Fisherman166/GM_Burnoff_Module/pcb_pictures/20211124_192147.jpg

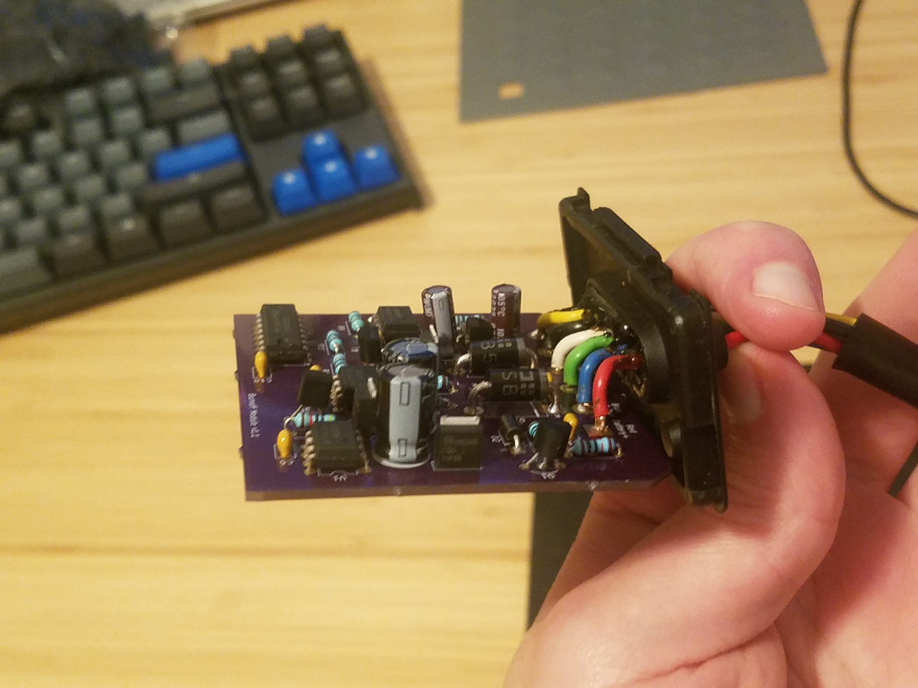
pcb_pictures/20211124_192147.jpg
