Fisherman166/GM_Burnoff_Module/pcb_pictures/20211023_175507.jpg

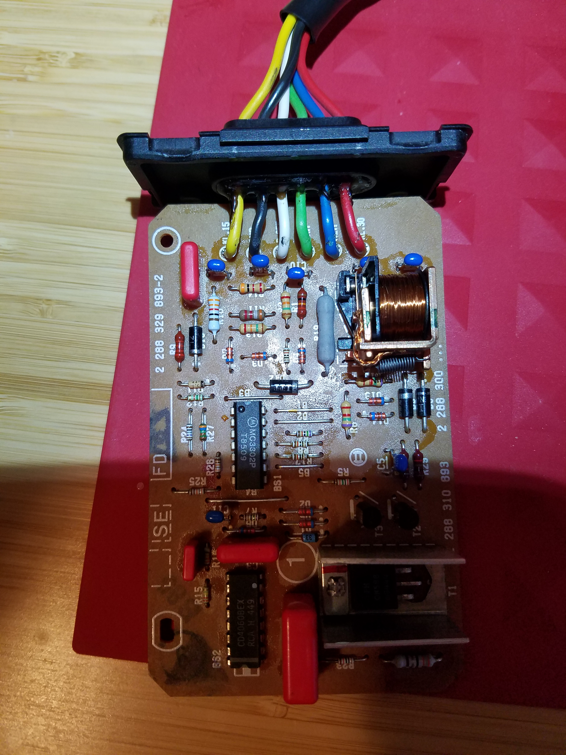
pcb_pictures/20211023_175507.jpg
